dennyzz/Pathfinder-v2/python/threadex.py

# from threading import Thread
# import threading
# import time

# global cycle
# cycle = 0.0

# class Hello5Program:  
#     def __init__(self):
#         self._running = True

#     def terminate(self):  
#         self._running = False  

#     def run(self):
#         global cycle
#         while self._running:
#             time.sleep(5) #Five second delay
#             cycle = cycle + 1.0
#             print( "5 Second Thread cycle+1.0 - ", cycle)

# class Hello2Program:  
#     def __init__(self):
#         self._running = True

#     def terminate(self):  
#         self._running = False  

#     def run(self):
#         global cycle
#         while self._running:
#             time.sleep(2) #Five second delay
#             cycle = cycle + 0.5
#             print( "2 Second Thread cycle+0.5 - ", cycle)

# #Create Class
# FiveSecond = Hello5Program()
# #Create Thread
# FiveSecondThread = Thread(target=FiveSecond.run) 
# #Start Thread 
# FiveSecondThread.start()

# #Create Class
# TwoSecond = Hello2Program()
# #Create Thread
# TwoSecondThread = Thread(target=TwoSecond.run) 
# #Start Thread 
# TwoSecondThread.start()


# Exit = False #Exit flag
# while Exit==False:
#  cycle = cycle + 0.1 
#  print ("Main Program increases cycle+0.1 - ", cycle)
#  time.sleep(1) #One second delay
#  if (cycle > 5): Exit = True #Exit Program

# TwoSecond.terminate()
# FiveSecond.terminate()
# print ("Goodbye :)")


# Instructions!
# scipy: the easiest install on windows is to use prebuilt wheels.
#   pip install wheel
#   then go to http://www.lfd.uci.edu/~gohlke/pythonlibs/#scipy
#   and download numpy+mkl and scipy
#   pip install those files
# for linux! 
# try sudo apt-get install python3-scipy python3-numpy


import time
import cv2
import numpy as np
import os
import scipy.signal
import sys
from scipy.optimize import curve_fit
from threading import Thread
import threading

exit = 0

def quadratic(x, a, b, c):
    return a * x * x + b * x + c

def d_quadratic(x, a, b):
    return 2*a*x + b

def cubic(x, a, b, c, d):
    return a * x * x * x + b * x * x + c * x + d

def quartic(x, a, b, c, d, e):
    return a * x * x * x * x + b * x * x * x + c * x * x + d * x + e

def exponential(x, a, b):
    return a**x + b

def line(p1, p2):
    A = (p1[1] - p2[1])
    B = (p2[0] - p1[0])
    C = (p1[0]*p2[1] - p2[0]*p1[1])
    return A, B, -C

def intersection(L1, L2):
    D  = L1[0] * L2[1] - L1[1] * L2[0]
    Dx = L1[2] * L2[1] - L1[1] * L2[2]
    Dy = L1[0] * L2[2] - L1[2] * L2[0]
    if D != 0:
        x = Dx / D
        y = Dy / D
        return x,y
    else:
        return False

def Thread_Cap(cap, buffer, flag, buff_lock):
    global exit
    while not exit:
        ret, frame = cap.read()
        buff_lock.acquire()
        # print("capture buffer locked")
        buffer[:] = frame
        # print(buffer)
        buff_lock.release()
        # print("capture buffer unlocked")
        # clear the stream in preparation for the next frame
        # rawCapture.truncate(0)
        flag.set()
        if not ret:
            exit = 1
            break

    cap.release()

def Thread_Process(buffer, flag, buff_lock):
    global exit
    w = 1/200
    b = -1/200

    ysize = buffer.shape[0]
    xsize = buffer.shape[1]

    frame = np.empty((ysize, xsize, 3), dtype=np.uint8)
    block_15_left = np.array([
    [b,b,b,b,b,b,b,b,b,b,b,b,b,b,b],
    [b,b,b,b,b,b,b,b,b,b,b,b,b,b,w],
    [b,b,b,b,b,b,b,b,b,b,b,b,b,w,w],
    [b,b,b,b,b,b,b,b,b,b,b,b,w,w,w],
    [b,b,b,b,b,b,b,b,b,b,b,w,w,w,w],
    [b,b,b,b,b,b,b,b,b,b,w,w,w,w,w],
    [b,b,b,b,b,b,b,b,b,w,w,w,w,w,w],
    [b,b,b,b,b,b,b,b,w,w,w,w,w,w,w],
    [b,b,b,b,b,b,b,w,w,w,w,w,w,w,w],
    [b,b,b,b,b,b,w,w,w,w,w,w,w,w,w],
    [b,b,b,b,b,w,w,w,w,w,w,w,w,w,w],
    [b,b,b,b,w,w,w,w,w,w,w,w,w,w,w],
    [b,b,b,w,w,w,w,w,w,w,w,w,w,w,w],
    [b,b,w,w,w,w,w,w,w,w,w,w,w,w,w],
    [b,w,w,w,w,w,w,w,w,w,w,w,w,w,w]
    ])
    block_15_right = np.array([
    [b,b,b,b,b,b,b,b,b,b,b,b,b,b,b],
    [w,b,b,b,b,b,b,b,b,b,b,b,b,b,b],
    [w,w,b,b,b,b,b,b,b,b,b,b,b,b,b],
    [w,w,w,b,b,b,b,b,b,b,b,b,b,b,b],
    [w,w,w,w,b,b,b,b,b,b,b,b,b,b,b],
    [w,w,w,w,w,b,b,b,b,b,b,b,b,b,b],
    [w,w,w,w,w,w,b,b,b,b,b,b,b,b,b],
    [w,w,w,w,w,w,w,b,b,b,b,b,b,b,b],
    [w,w,w,w,w,w,w,w,b,b,b,b,b,b,b],
    [w,w,w,w,w,w,w,w,w,b,b,b,b,b,b],
    [w,w,w,w,w,w,w,w,w,w,b,b,b,b,b],
    [w,w,w,w,w,w,w,w,w,w,w,b,b,b,b],
    [w,w,w,w,w,w,w,w,w,w,w,w,b,b,b],
    [w,w,w,w,w,w,w,w,w,w,w,w,w,b,b],
    [w,w,w,w,w,w,w,w,w,w,w,w,w,w,b]
    ])
    block_15_left_flip = np.array([
    [b,w,w,w,w,w,w,w,w,w,w,w,w,w,w],
    [b,b,w,w,w,w,w,w,w,w,w,w,w,w,w],
    [b,b,b,w,w,w,w,w,w,w,w,w,w,w,w],
    [b,b,b,b,w,w,w,w,w,w,w,w,w,w,w],
    [b,b,b,b,b,w,w,w,w,w,w,w,w,w,w],
    [b,b,b,b,b,b,w,w,w,w,w,w,w,w,w],
    [b,b,b,b,b,b,b,w,w,w,w,w,w,w,w],
    [b,b,b,b,b,b,b,b,w,w,w,w,w,w,w],
    [b,b,b,b,b,b,b,b,b,w,w,w,w,w,w],
    [b,b,b,b,b,b,b,b,b,b,w,w,w,w,w],
    [b,b,b,b,b,b,b,b,b,b,b,w,w,w,w],
    [b,b,b,b,b,b,b,b,b,b,b,b,w,w,w],
    [b,b,b,b,b,b,b,b,b,b,b,b,b,w,w],
    [b,b,b,b,b,b,b,b,b,b,b,b,b,b,w],
    [b,b,b,b,b,b,b,b,b,b,b,b,b,b,b]
    ])
    block_15_right_flip = np.array([
    [w,w,w,w,w,w,w,w,w,w,w,w,w,w,b],
    [w,w,w,w,w,w,w,w,w,w,w,w,w,b,b],
    [w,w,w,w,w,w,w,w,w,w,w,w,b,b,b],
    [w,w,w,w,w,w,w,w,w,w,w,b,b,b,b],
    [w,w,w,w,w,w,w,w,w,w,b,b,b,b,b],
    [w,w,w,w,w,w,w,w,w,b,b,b,b,b,b],
    [w,w,w,w,w,w,w,w,b,b,b,b,b,b,b],
    [w,w,w,w,w,w,w,b,b,b,b,b,b,b,b],
    [w,w,w,w,w,w,b,b,b,b,b,b,b,b,b],
    [w,w,w,w,w,b,b,b,b,b,b,b,b,b,b],
    [w,w,w,w,b,b,b,b,b,b,b,b,b,b,b],
    [w,w,w,b,b,b,b,b,b,b,b,b,b,b,b],
    [w,w,b,b,b,b,b,b,b,b,b,b,b,b,b],
    [w,b,b,b,b,b,b,b,b,b,b,b,b,b,b],
    [b,b,b,b,b,b,b,b,b,b,b,b,b,b,b]
    ])

    block_left = block_15_left
    block_right = block_15_right 
    block_left_flip = block_15_left_flip
    block_right_flip = block_15_right_flip
    blocksize = 15
    halfblock = int(np.floor(blocksize/2))

    scanwidth = 300
    scanwidthmin = 100
    scanheight = 15
    scanspacing = 15
    scanlines = 40
    threshold = 1
    # value for minimum number of good edges detected for curve fitting 
    min_data_good = 6
    # pixels from the bottom that the scanlines first index starts from
    scanstartline = 150


    green = (0,255,0)
    red = (0,0,255)
    blue = (255,0,0)
    yellow = (0,255,255)
    orange = (51, 153, 255)
    laneleft = np.empty((scanlines,2), dtype = np.int32)
    laneright= np.empty((scanlines,2), dtype = np.int32)
    laneleftcount = 0
    lanerightcount = 0

    # angle and offset datas used for course correction
    leftangle = 0
    rightangle = 0
    leftx = xsize/2
    rightx = xsize/2
    while not exit:
        flag.wait()
        buff_lock.acquire()
        print("process buffer locked")
        # print(buffer)
        frame[:] = buffer
        buff_lock.release()
        print("process buffer unlocked")
        # start_pre_time = time.time()
        # step1: grayscale
        gray = cv2.cvtColor(frame, cv2.COLOR_BGR2GRAY)

        # step2: define top left corner of starting scan block
        L_index = [0,ysize-scanstartline]
        R_index = [xsize-300, ysize-scanstartline]

        # reset some parameters
        leftblob = np.empty((scanlines*15, 286))
        rightblob = np.empty((scanlines*15, 286))
        scanwidthl = scanwidth
        scanwidthr = scanwidth
        laneleftcount = 0
        lanerightcount = 0

        # begin algo timing

        # proc_pre_time = (time.time() - start_pre_time) * 1000

        # start_algo_time = time.time()
    ####### main process loop
        # for loop controls how many blocks vertically are checked
        for x in range(0,scanlines):

            # step3: grab the proper block of pixels for the current scan block
            leftscan = gray[L_index[1]:L_index[1]+scanheight , L_index[0]:L_index[0] + scanwidthl]
            rightscan = gray[R_index[1]:R_index[1]+scanheight , R_index[0]:R_index[0] + scanwidthr]
            # cv2.imshow("left", leftscan)
            # cv2.imshow("right", rightscan)

            # step4: run the correlation/eigenvalue/convolution thing
            left = scipy.signal.correlate2d(leftscan, block_left, mode='valid')[0]
            right = scipy.signal.correlate2d(rightscan, block_right, mode='valid')[0]

            # step 4.5 if it returns nothing of adequate similarity, try the reversed masks
            if max(left) < threshold:
                left = scipy.signal.correlate2d(leftscan, block_left_flip, mode='valid')[0]
            if max(right) < threshold:
                right = scipy.signal.correlate2d(rightscan, block_right_flip, mode='valid')[0]

            # f.write('leftmax:' + str(np.max(left)) + ' ' + str(np.min(left)) + '\n')
            # f.write('rightmax:' + str(np.max(right)) + ' ' + str(np.min(right)) + '\n')
            # copy for visualization
            np.copyto(leftblob[(scanlines-x-1)*15:(scanlines-x)*15, 0:left.shape[0]], left)
            np.copyto(rightblob[(scanlines-x-1)*15:(scanlines-x)*15, 0:right.shape[0]], right)

            # so idxL/R is the index of the max thing, or the best boundary location as an x offset from the scan box width
            # idxLRf is the location of the box in the frame
            # L_index and R_index are the top left point of the scan box.
            
            if True:
                # left and right at this point contain a line of values corresponding to all valid correlation overlaps
                # thus the index is the center of each block, which means within each scan block, the center of the max block is (idxl+7, 7)
                idxl = np.argmax(left)
                idxr = np.argmax(right)

                # idxl-f stands for the index in the actual frame, this converts our idxl location to the correct pixel location on the full input
                idxlf = (halfblock + idxl + L_index[0], L_index[1] + halfblock)
                idxrf = (halfblock + idxr + R_index[0] , R_index[1] + halfblock)
                # print("left at frame loc:"+str(idxlf))
                # print("right at frame loc:"+str(idxrf))
                
                # draw the green scan box, and the red/blue locators
                cv2.rectangle(frame, tuple(L_index), (L_index[0] + scanwidthl, L_index[1] + scanheight-1), green, 2)
                cv2.rectangle(frame, tuple(R_index), (R_index[0] + scanwidthr, R_index[1] + scanheight-1), green, 2)

                # move the bounding box to next position by scanspacing pixels
                if left[idxl] < threshold:
                    # if cannot find lane line
                    if scanwidthl == scanwidthmin: # if from good to failing
                        L_index[0] = int(L_index[0] - ((scanwidth - scanwidthmin) / 2))
                    cv2.rectangle(frame, (idxlf[0]-halfblock, idxlf[1]-halfblock), (idxlf[0]+halfblock, idxlf[1]+halfblock), yellow, 2)
                    scanwidthl = scanwidth
                    # print("left BAD")
                    L_index = [L_index[0], L_index[1] - scanspacing]
                else:
                    laneleft[laneleftcount] = idxlf
                    laneleftcount += 1
                    cv2.rectangle(frame, (idxlf[0]-halfblock, idxlf[1]-halfblock), (idxlf[0]+halfblock, idxlf[1]+halfblock), red, 2)
                    grayblock = gray[(idxlf[1]-halfblock):(idxlf[1]+halfblock+1), (idxlf[0]-halfblock):(idxlf[0]+halfblock+1)]
                    # gray[(idxlf[1]-halfblock):(idxlf[1]+halfblock+1), (idxlf[0]-halfblock):(idxlf[0]+halfblock+1)] = cv2.adaptiveThreshold(grayblock, 255, cv2.ADAPTIVE_THRESH_MEAN_C, cv2.THRESH_BINARY, blocksize, 0)
                    ret, gray[(idxlf[1]-halfblock):(idxlf[1]+halfblock+1), (idxlf[0]-halfblock):(idxlf[0]+halfblock+1)] = cv2.threshold(grayblock, 0, 255, cv2.THRESH_BINARY+cv2.THRESH_OTSU)
                    scanwidthl = scanwidthmin
                    L_index = [idxlf[0] - int(scanwidthl/2), idxlf[1] - halfblock - scanspacing]
                if right[idxr] < threshold:
                    cv2.rectangle(frame, (idxrf[0]-halfblock, idxrf[1]-halfblock), (idxrf[0]+halfblock, idxrf[1]+halfblock), yellow, 2)
                    scanwidthr = scanwidth
                    # print("right BAD")
                    R_index = [R_index[0], R_index[1] - scanspacing]    
                else:
                    laneright[lanerightcount] = idxrf
                    lanerightcount += 1
                    cv2.rectangle(frame, (idxrf[0]-halfblock, idxrf[1]-halfblock), (idxrf[0]+halfblock, idxrf[1]+halfblock), blue, 2)
                    grayblock = gray[(idxrf[1]-halfblock):(idxrf[1]+halfblock+1), (idxrf[0]-halfblock):(idxrf[0]+halfblock+1)]
                    # gray[(idxrf[1]-halfblock):(idxrf[1]+halfblock+1), (idxrf[0]-halfblock):(idxrf[0]+halfblock+1)] = cv2.adaptiveThreshold(grayblock, 255, cv2.ADAPTIVE_THRESH_MEAN_C, cv2.THRESH_BINARY, blocksize, 0)
                    ret, gray[(idxrf[1]-halfblock):(idxrf[1]+halfblock+1), (idxrf[0]-halfblock):(idxrf[0]+halfblock+1)] = cv2.threshold(grayblock, 0, 255, cv2.THRESH_BINARY+cv2.THRESH_OTSU)
                    scanwidthr = scanwidthmin
                    R_index = [idxrf[0] - int(scanwidthr/2), idxrf[1] - halfblock - scanspacing]

                if L_index[0] < 0:
                    L_index[0] = 0
                if R_index[0] > xsize-scanwidthr:
                    R_index[0] = xsize-scanwidthr

        ####### end processing
        # proc_algo_time = (time.time() - start_algo_time)*1000
        ####### end processing



        #reconstruct line segments?
        leftblob = np.multiply(leftblob, 0.1)
        rightblob = np.multiply(rightblob, 0.1)

        # start_post_time = time.time()

        if(laneleftcount > min_data_good):
            # flip the axes to get a real function
            x = laneleft[0:laneleftcount, 1]
            y = laneleft[0:laneleftcount, 0]
            popt, pcov = curve_fit(quadratic, x, y)

            prevpoint = (int(quadratic(0, popt[0], popt[1], popt[2])), 0)
            for y in range(10, ysize, 10):
                x = int(quadratic(y, popt[0], popt[1], popt[2]))
                cv2.line(frame,prevpoint,(x,y),orange,2)
                prevpoint = (x,y)

            # offset computed from curve fit at scan start location
            leftx = xsize/2 - quadratic(ysize-scanstartline, popt[0], popt[1], popt[2])
            # angle computed from tangent of curve fit at scan start location
            slope = d_quadratic(ysize-scanstartline, popt[0], popt[1])
            rads = np.arctan(slope)
            leftangle = rads/np.pi*180
        if(lanerightcount > min_data_good):
            # popt, pcov = curve_fit(quadratic, x, y)
            x = laneright[0:lanerightcount, 1]
            y = laneright[0:lanerightcount, 0]
            popt, pcov = curve_fit(quadratic, x, y)
            x = 0
            y = quadratic(0, popt[0], popt[1], popt[2])
            prevpoint = (int(quadratic(0, popt[0], popt[1], popt[2])), 0)
            for y in range(10, ysize, 10):
                x = int(quadratic(y, popt[0], popt[1], popt[2]))
                cv2.line(frame,prevpoint,(x,y),orange,2)
                prevpoint = (x,y)

            # offset computed from curve fit at scan start location
            rightx = quadratic(ysize-scanstartline, popt[0], popt[1], popt[2]) - xsize/2
            # angle computed from tangent of curve fit at scan start location
            slope = d_quadratic(ysize-scanstartline, popt[0], popt[1])
            rads = np.arctan(slope)
            rightangle = rads/np.pi*180

        offset = leftx - rightx 
        angle = ((rightangle + leftangle)/2)
        # proc_post_time = (time.time() - start_post_time)*1000

        cv2.imshow('frame', frame)
        cv2.imshow('left', leftblob)
        cv2.imshow('right', rightblob)
        key = cv2.waitKey(1) & 0xFF


#################### end of Thread_Process






# main is the output task!
cap = cv2.VideoCapture("footage/0degree.mp4 ")
# cap = cv2.VideoCapture("footage/radius2angle75.mp4")
# cap = cv2.VideoCapture("footage/rootbeercar.mp4 ")

blah, temp = cap.read()
ysize = temp.shape[0]
xsize = temp.shape[1]
img_buf = np.empty((ysize, xsize, 3), dtype=np.uint8)

image_ready = threading.Event()
distance_ready = threading.Event()
image_buffer_lock = threading.Lock()


# start threads
Process_Thread = threading.Thread(target=Thread_Process, args=(img_buf, image_ready, image_buffer_lock))
Capture_Thread = threading.Thread(target=Thread_Cap, args=(cap, img_buf, image_ready, image_buffer_lock))
Distance_Thread = threading.Thread()
print("threads created")

Process_Thread.start()
Capture_Thread.start()
print("threads started")
# start_time = time.time()
while True:

    image_ready.wait()
    # # proc_time = (time.time() - start_time)*1000
    # if smooth_time == 0:
    #     smooth_time = proc_time
    # else:
    #     smooth_time = 0.9*smooth_time + 0.1*proc_time
        
    # if proc_algo_time_s == 0:
    #     proc_algo_time_s = proc_algo_time
    # else:
    #     proc_algo_time_s = 0.9*proc_algo_time_s + 0.1*proc_algo_time
        
    # if proc_post_time_s == 0:
    #     proc_post_time_s = proc_post_time
    # else:
    #     proc_post_time_s = 0.9*proc_post_time_s + 0.1*proc_post_time
        
    # if proc_pre_time_s == 0:
    #     proc_pre_time_s = proc_pre_time
    # else:
    #     proc_pre_time_s = 0.9*proc_pre_time_s + 0.1*proc_pre_time
        
    # fps_calc = int(1000/smooth_time)
    # sys.stdout.write("\rtimetot:%dmS fps:%d algotime:%dmS posttime:%dmS pretime:%dmS       " %(smooth_time, fps_calc, proc_algo_time_s, proc_post_time_s, proc_pre_time_s))
    # sys.stdout.write("\rtime:%dmS, fps:%d off: %d left:%.1fdeg right:%.1fdeg angle:%d      " % (smooth_time, fps_calc, offset, leftangle, rightangle, angle))
    sys.stdout.flush()
    #time it from here
    start_time = time.time()
    #if the `q` key was pressed, break from the loop
    if key == ord("n"):
        print("next")
        next = 1
    if key == ord("q"):
        exit = 1
        break

Process_Thread.join()
Capture_Thread.join()

print("threads ended, exited normally")

sys.exit(0)
