dennyzz/Pathfinder-v2/python/lcd8+LED.py

#!/usr/bin/python

from subprocess import *
from time import sleep, strftime
from datetime import datetime
import Adafruit_CharLCD
import Adafruit_GPIO as GPIO
import time
import string
import pathfindershield

rs = 26
rw = 19
en = 13
d4 = 12
d5 = 16
d6 = 20
d7 = 21
v0 = 6
cols = 8
lines = 2

pathfindershield.motorservoledcmd(0)
sleep(1)
pathfindershield.motorservoledcmd(0xff)
sleep(1)
pathfindershield.motorservoledcmd(0)
gpio=GPIO.get_platform_gpio()
gpio.setup(rw, GPIO.OUT)
gpio.output(rw, False)
gpio.setup(v0, GPIO.OUT)
sleep(1)
lcd = Adafruit_CharLCD.Adafruit_CharLCD(rs, en, d4, d5, d6, d7, cols, lines)
lcd.clear()

cmd = "ip addr show wlan0 | grep -m 1 inet | awk '{print $2}' | cut -d/ -f1"


def run_cmd(cmd):
        p = Popen(cmd, shell=True, stdout=PIPE)
        output = p.communicate()[0]
        return output

while True:
        lcd.home()
        ipaddr = run_cmd(cmd)
        ips = string.split(ipaddr, '.')
        if len(ips) == 4:
                ip1 = '%s.%s' % (ips[0], ips[1]) 
                ip2 = '%s.%s' % (ips[2], ips[3].rstrip())
                ip1 = 'i%7s\n' % (ip1)
                ip2 = 'p%7s\n' % (ip2)
                lcd.message(ip1)
                lcd.message(ip2)
        else:
                lcd.message('   no   \n')
                lcd.message('network!')
        sleep(1)
