dennyzz/Pathfinder-v2/python/captures.py

raspivid -t 15000 -w 1280 -h 1024 -fps 25 -b 1200000 -p 0,0,1280,1024 -o pivideo.h264
MP4Box -add pivideo.h264 pivideo.mp4

angles are approximate at 8 inches high

roootbeer is 5in at approx 45 degrees

boxes is 45 ish degress at 6 inches high
